sq5nry/qo100-pluto-heavy-duty-gs/hw-pluto-ext-clock/pluto_clock_buffer-3d.png

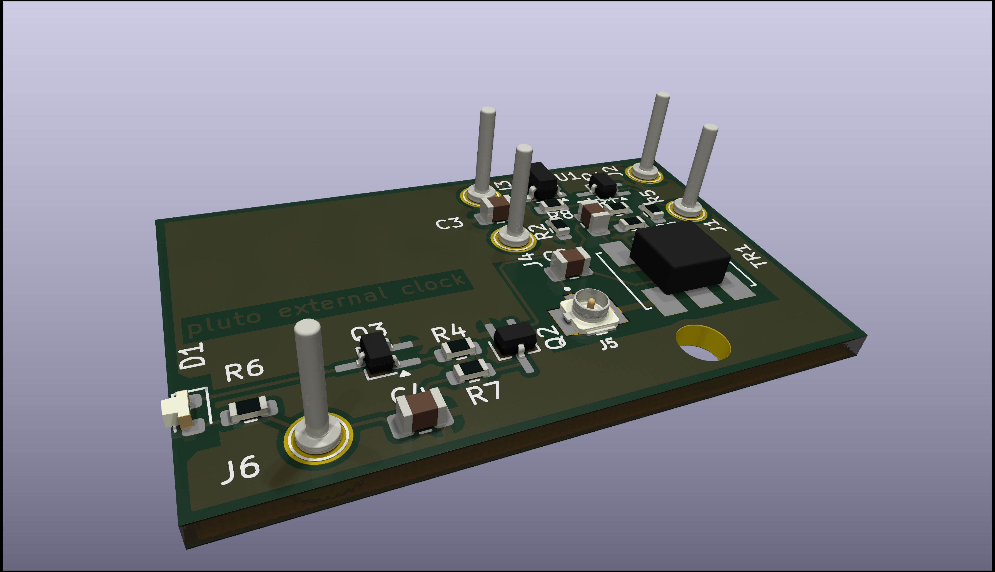
hw-pluto-ext-clock/pluto_clock_buffer-3d.png
