sq5nry/qo100-pluto-heavy-duty-gs/hw-pluto-ext-clock/pluto_clock_buffer-pcb.png

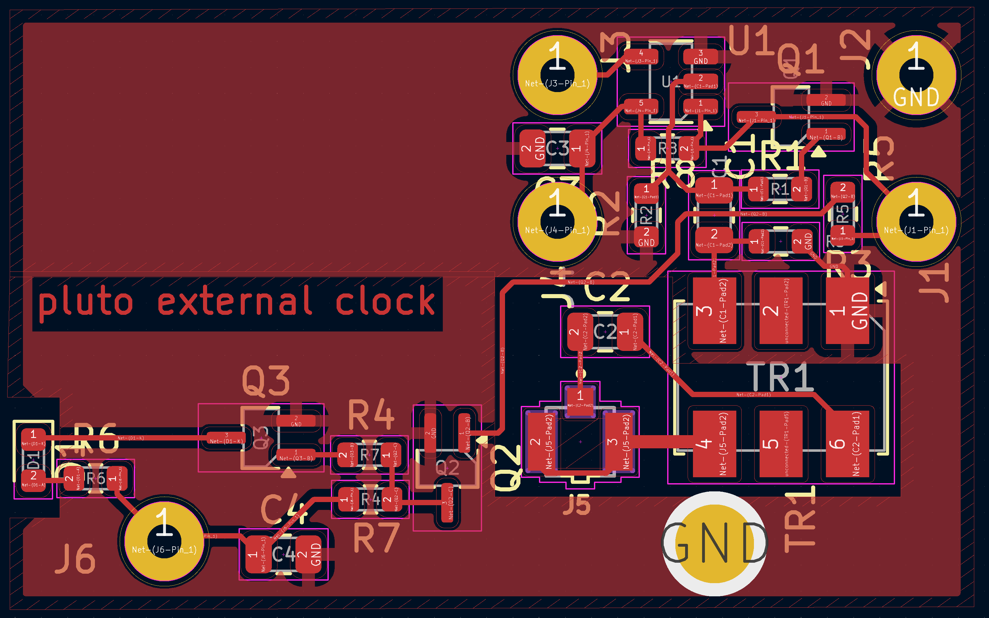
hw-pluto-ext-clock/pluto_clock_buffer-pcb.png
