sq5nry/qo100-pluto-heavy-duty-gs/pics/eth_wiring_1.jpg

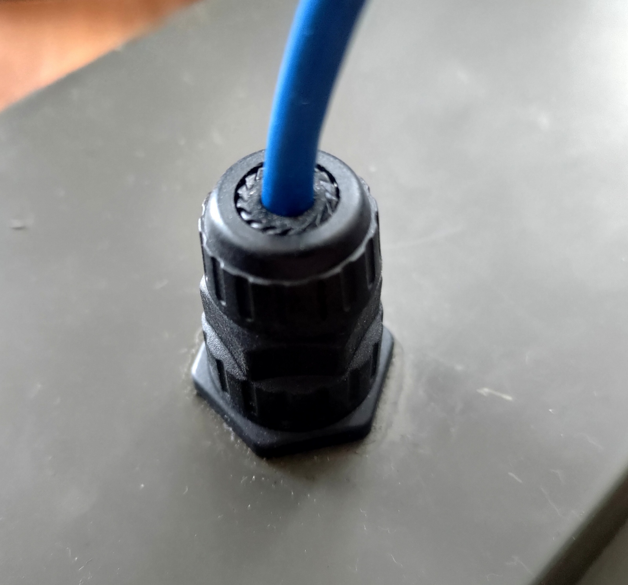
pics/eth_wiring_1.jpg
