sq5nry/qo100-pluto-heavy-duty-gs/pics/humidity_measurements.png

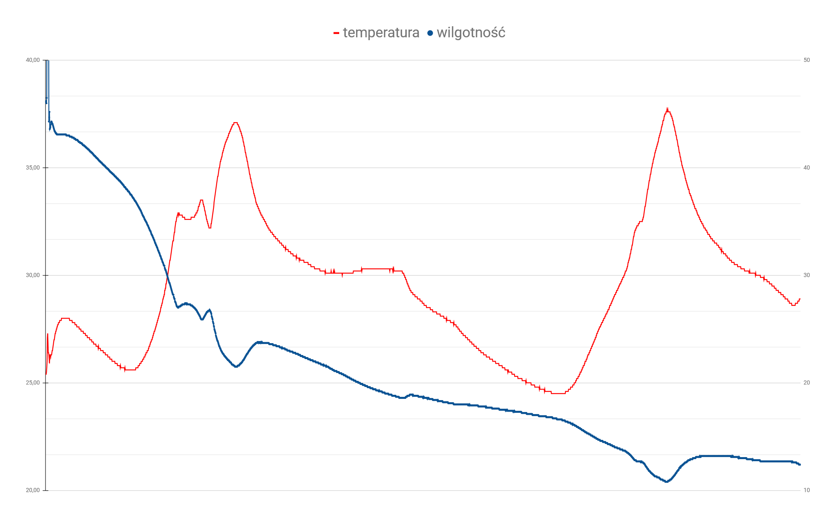
pics/humidity_measurements.png
